mrkingseasheep/PixApple/img/14.png

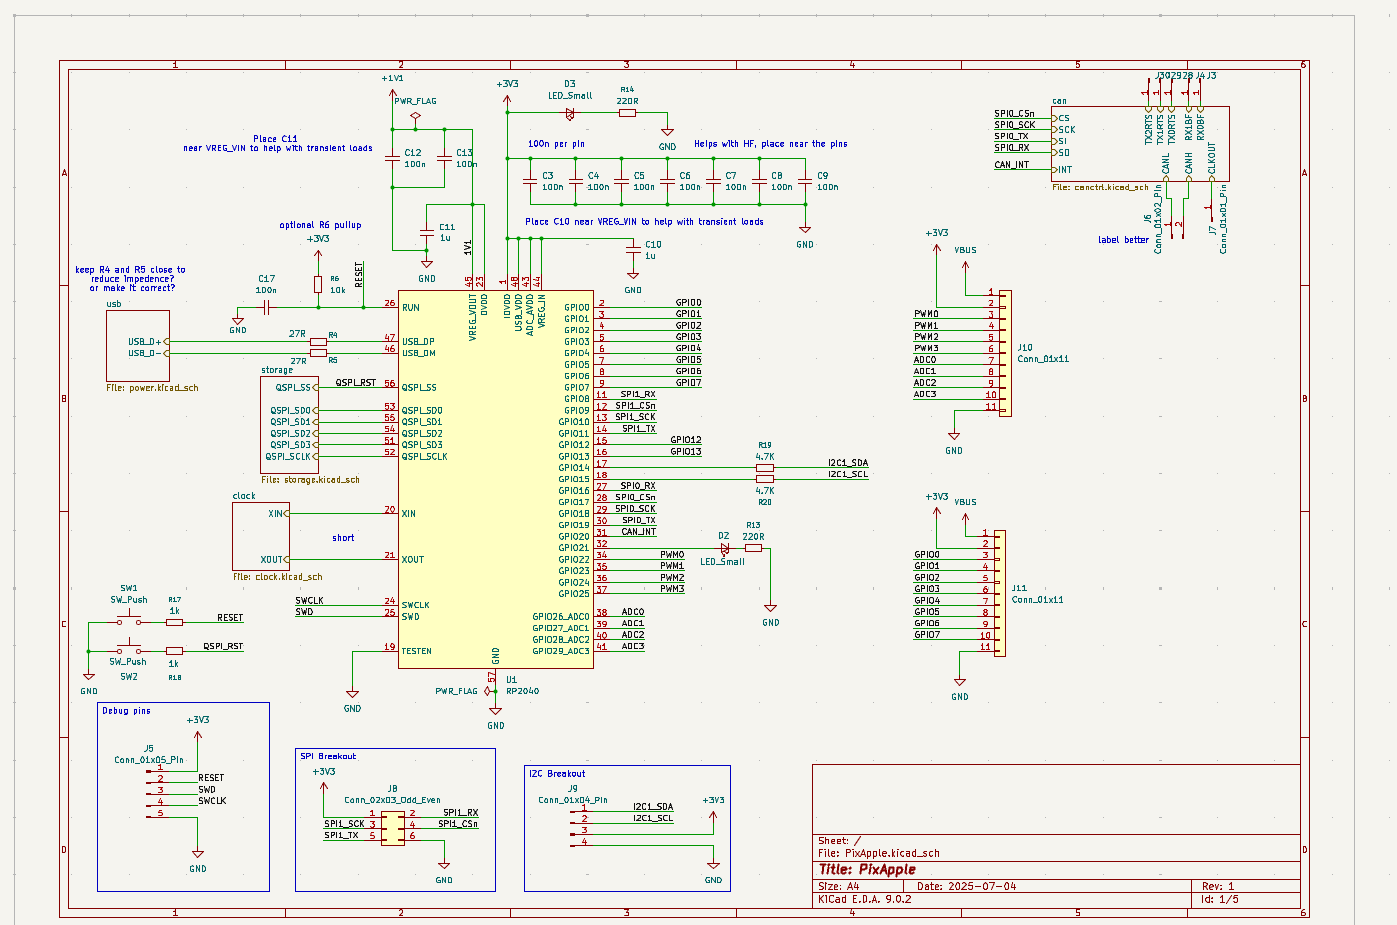
img/14.png
